devangshu/GripSimulator/esp8266/glove/glove.h

/* grip simulator glove device mqtt client driver */

#ifndef __GS_GLOVE_H__
#define __GS_GLOVE_H__

#define DEBUG true
#define DEBUG_VERBOSE true

#define WIFI_PASS "8372681759362047"

#define API_URL "mqtt.anuv.me"	// "test.mosquitto.org"
#define API_PORT 1883

#define DEVICE_NUM 0
#define DEVICE_NAME "glove"

#endif
