devangshu/GripSimulator/esp8266/model/model.h

/* grip simulator model device mqtt client driver */

#ifndef __GS_MODEL_H__
#define __GS_MODEL_H__

#define DEBUG false
#define DEBUG_VERBOSE false

#define WIFI_PASS "0335803293960677"

#define API_URL "mqtt.anuv.me"	// "test.mosquitto.org"
#define API_PORT 1883

#define DEVICE_NUM 1
#define DEVICE_NAME "model"

#endif
