devangshu/GripSimulator/tm4c123/inc/MAX5353.c

// MAX5353.c
// Runs on LM4F120/TM4C123
// Use SSI0 to send a 16-bit code to the MAX5353.
// Daniel Valvano
// September 11, 2013

/* This example accompanies the book
   "Embedded Systems: Real Time Interfacing to Arm Cortex M Microcontrollers",
   ISBN: 978-1463590154, Jonathan Valvano, copyright (c) 2015

 Copyright 2015 by Jonathan W. Valvano, valvano@mail.utexas.edu
    You may use, edit, run or distribute this file
    as long as the above copyright notice remains
 THIS SOFTWARE IS PROVIDED "AS IS".  NO WARRANTIES, WHETHER EXPRESS, IMPLIED
 OR STATUTORY, INCLUDING, BUT NOT LIMITED TO, IMPLIED WARRANTIES OF
 MERCHANTABILITY AND FITNESS FOR A PARTICULAR PURPOSE APPLY TO THIS SOFTWARE.
 VALVANO SHALL NOT, IN ANY CIRCUMSTANCES, BE LIABLE FOR SPECIAL, INCIDENTAL,
 OR CONSEQUENTIAL DAMAGES, FOR ANY REASON WHATSOEVER.
 For more information about my classes, my research, and my books, see
 http://users.ece.utexas.edu/~valvano/
 */

// SSI0Clk (SCLK, pin 4) connected to PA2
// SSI0Fss (!CS, pin 2) connected to PA3
// SSI0Tx (DIN, pin 3) connected to PA5
// see Figure 7.19 for complete schematic
#include <stdint.h>
#include "../inc/tm4c123gh6pm.h"


//********DAC_Init*****************
// Initialize Max5353 12-bit DAC
// inputs:  initial voltage output (0 to 4095)
// outputs: none
// assumes: system clock rate less than 20 MHz
void DAC_Init_Max(uint16_t data){
  SYSCTL_RCGCSSI_R |= 0x01;       // activate SSI0
  SYSCTL_RCGCGPIO_R |= 0x01;      // activate port A
  while((SYSCTL_PRGPIO_R&0x01) == 0){};// ready?
  GPIO_PORTA_AFSEL_R |= 0x2C;     // enable alt funct on PA2,3,5
  GPIO_PORTA_DEN_R |= 0x2C;       // configure PA2,3,5 as SSI
  GPIO_PORTA_PCTL_R = (GPIO_PORTA_PCTL_R&0xFF0F00FF)+0x00202200;
  GPIO_PORTA_AMSEL_R = 0;         // disable analog functionality on PA
  SSI0_CR1_R = 0x00000000;        // disable SSI, master mode
  SSI0_CPSR_R = 0x02;             // 8 MHz SSIClk 
  SSI0_CR0_R &= ~(0x0000FFF0);    // SCR = 0, SPH = 0, SPO = 0 Freescale
  SSI0_CR0_R |= 0x0F;             // DSS = 16-bit data
  SSI0_DR_R = data;               // load 'data' into transmit FIFO
  SSI0_CR1_R |= 0x00000002;       // enable SSI

}

//********DAC_Init*****************
// Initialize TLV5616 12-bit DAC
// assumes bus clock is 80 MHz
// inputs: initial voltage output (0 to 4095)
// outputs:none

void DAC_Init(uint16_t data){
  SYSCTL_RCGCSSI_R |= 0x02;       // activate SSI1
  SYSCTL_RCGCGPIO_R |= 0x08;      // activate port D
  
  while((SYSCTL_PRGPIO_R&0x08) == 0){}; // ready?
  SSI1_CR1_R = 0x00000000;        // disable SSI, master mode
  GPIO_PORTD_AFSEL_R |= 0x0B;     // enable alt funct on PD3,1,0
  GPIO_PORTD_DEN_R |= 0x0B;       // enable digital I/O on PD3,1,0
  GPIO_PORTD_PCTL_R = (GPIO_PORTD_PCTL_R
                     & 0xFFFF0F00)
                     + 0x00002022;
  GPIO_PORTD_AMSEL_R &= ~0x0B;    // disable analog functionality on PD
  SSI1_CPSR_R = 0x08;             // 80MHz/8 = 10 MHz SSIClk (should work up to 20 MHz)
  SSI1_CR0_R &= ~(0x0000FFF0);    // SCR = 0, SPH = 0, SPO = 1 Freescale
  SSI1_CR0_R += 0x40;             // SPO = 1
  SSI1_CR0_R |= 0x0F;             // DSS = 16-bit data
  SSI1_DR_R = data;               // load 'data' into transmit FIFO
  SSI1_CR1_R |= 0x00000002;       // enable SSI
}




//********DAC_Out*****************
// Send data to Max5353 12-bit DAC
// inputs:  voltage output (0 to 4095)
// outputs: none
void DAC_Out(uint16_t code){   
  while((SSI1_SR_R&0x00000002)==0){};// SSI Transmit FIFO Not Full
  SSI1_DR_R = code; }                // data out, no reply
  
//********DAC_Out*****************
// Send data to Max5353 12-bit DAC
// inputs:  voltage output (0 to 4095)
// outputs: reply is returned
// send the 16-bit code to the SSI, return a reply
uint16_t DAC_Out2(uint16_t code){   uint16_t receive;
  while((SSI0_SR_R&0x00000002)==0){};// SSI Transmit FIFO Not Full
  SSI0_DR_R = code;                  // data out
  while((SSI0_SR_R&0x00000004)==0){};// SSI Receive FIFO Not Empty
  receive = SSI0_DR_R;               // acknowledge response
  return receive;
}

void DAC_InitRaw(void){
  SYSCTL_RCGCSSI_R |= 0x01;       // activate SSI0
  SYSCTL_RCGCGPIO_R |= 0x01;      // activate port A
  while((SYSCTL_PRGPIO_R&0x01) == 0){};// ready?
  GPIO_PORTA_AFSEL_R |= 0x24;     // enable alt funct on PA2,5, regular GPIO on PA3
  GPIO_PORTA_DEN_R |= 0x2C;       // configure PA2,5 as SSI, PA3 is regular GPIO
  GPIO_PORTA_DATA_R |= 0x08;      // PA3 FSS high
  GPIO_PORTA_PCTL_R = (GPIO_PORTA_PCTL_R&0xFF0F00FF)+0x00200200;
  GPIO_PORTA_AMSEL_R = 0;         // disable analog functionality on PA
  SSI0_CR1_R = 0x00000000;        // disable SSI, master mode
  SSI0_CPSR_R = 0x02;             // 8 MHz SSIClk 
  SSI0_CR0_R &= ~(0x0000FFF0);    // SCR = 0, SPH = 0, SPO = 0 Freescale
  SSI0_CR0_R |= 0x0F;             // DSS = 16-bit data
  SSI0_CR1_R |= 0x00000002;       // enable SSI

}
//********DAC_Out*****************
// Send data to Max5353 12-bit DAC
// inputs:  voltage output (0 to 4095)
// outputs: none
// send the 16-bit code to the SSI, 
void DAC_OutRaw(uint16_t code){  
  GPIO_PORTA_DATA_R &= ~0x08;        // PA3 FSS low
  
  while((SSI0_SR_R&0x00000002)==0){};// SSI Transmit FIFO Not Full
  SSI0_DR_R = code;                  // data out

  GPIO_PORTA_DATA_R |= 0x08;         // PA3 FSS high
}
