devangshu/GripSimulator/esp8266/common.h

/* grip simulator common device client config */

#ifndef __GS_COMMON_H__
#define __GS_COMMON_H__

#include <Arduino.h>
#include <ESP8266WiFi.h>
#include <NTPClient.h>
#include <PubSubClient.h>
#include <WiFiUdp.h>

//#define WIFI_SSID "21 Resident"
//#define WIFI_PASS "Hookem*2101"
#define WIFI_SSID "utexas-iot"

#define TIME_SERVER "pool.ntp.org"
#define MQTT_CLIENT_ID "gripsim_445l_client"

#define VIRTUALPIN_COUNT 5
#define VIRTUALPIN_TOPIC "virtualpin"
#define VIRTUALPIN_TOPIC_LEN 10

#define MSGBUFF_MAXLEN 500

#define BRIGHTNESS_MIN 0
#define BRIGHTNESS_MAX PWMRANGE	 // 1023 or 255

/* utilities */
// generic
int bound_integer(int value, int minimum, int maximum) {
	if (value < minimum) value = minimum;
	if (value > maximum) value = maximum;
	return value;
}
// led control
int correct_brightness(int brightness) {
	return bound_integer(brightness, BRIGHTNESS_MIN, BRIGHTNESS_MAX);
}
void led_out(int led_pin, int brightness) {
	brightness = correct_brightness(brightness);
	analogWrite(led_pin, brightness);
}
void led_out_builtin(int led_b_pin, int brightness) {
	brightness = correct_brightness(brightness);
	brightness = BRIGHTNESS_MAX - (brightness - BRIGHTNESS_MIN);
	analogWrite(led_b_pin, brightness);
}

#endif
