devangshu/GripSimulator/tm4c123/src/GripSimulator-Glove/TimerDriver.c

/* Timer Driver Module */

#include "TimerDriver.h"

/* constants */

#define PF1 (*((volatile uint32_t *)0x40025008))
#define PF2 (*((volatile uint32_t *)0x40025010))

/* module direct imports */

/* module fields */

/* module internal functions */

void Timer0_Init(void) {
	volatile uint32_t delay;
	// **** general initialization ****
	SYSCTL_RCGCTIMER_R |= 0x01;		  // activate timer0
	delay = SYSCTL_RCGCTIMER_R;		  // allow time to finish activating
	TIMER0_CTL_R &= ~TIMER_CTL_TAEN;  // disable timer0A during setup
	TIMER0_CFG_R = 0;				  // configure for 32-bit timer mode
	// **** timer0A initialization ****
	// configure for periodic mode
	TIMER0_TAMR_R = TIMER_TAMR_TAMR_PERIOD;
	TIMER0_TAILR_R = (80000 / 2) - 1;
	TIMER0_IMR_R |= TIMER_IMR_TATOIM;	// enable timeout (rollover) interrupt
	TIMER0_ICR_R = TIMER_ICR_TATOCINT;	// clear timer0A timeout flag
										//TIMER0_TAPR_R = 0;
	TIMER0_CTL_R |= TIMER_CTL_TAEN;		// enable timer0A 32-b, periodic, interrupts
	// **** interrupt initialization ****
	// Timer0A=priority 2
	NVIC_PRI4_R = (NVIC_PRI4_R & 0x00FFFFFF) | 0x40000000;	// top 3 bits
	NVIC_EN0_R = 1 << 19;									// enable interrupt 19 in NVIC
}
void Timer0A_Init100HzInt(void) {
	volatile uint32_t delay;
	// **** general initialization ****
	SYSCTL_RCGCTIMER_R |= 0x01;		  // activate timer0
	delay = SYSCTL_RCGCTIMER_R;		  // allow time to finish activating
	TIMER0_CTL_R &= ~TIMER_CTL_TAEN;  // disable timer0A during setup
	TIMER0_CFG_R = 0;				  // configure for 32-bit timer mode
	// **** timer0A initialization ****
	// configure for periodic mode
	TIMER0_TAMR_R = TIMER_TAMR_TAMR_PERIOD;
	TIMER0_TAILR_R = 799999;			// start value for 100 Hz interrupts
	TIMER0_IMR_R |= TIMER_IMR_TATOIM;	// enable timeout (rollover) interrupt
	TIMER0_ICR_R = TIMER_ICR_TATOCINT;	// clear timer0A timeout flag
	TIMER0_CTL_R |= TIMER_CTL_TAEN;		// enable timer0A 32-b, periodic, interrupts
	// **** interrupt initialization ****
	// Timer0A=priority 2
	NVIC_PRI4_R = (NVIC_PRI4_R & 0x00FFFFFF) | 0x40000000;	// top 3 bits
	NVIC_EN0_R = 1 << 19;									// enable interrupt 19 in NVIC
}
void Timer1_Init(void) {
	volatile uint32_t delay;
	SYSCTL_RCGCTIMER_R |= 0x02;								// 0) activate TIMER1
	delay = SYSCTL_RCGCTIMER_R;								// allow time to finish activating
	TIMER1_CTL_R = 0x00000000;								// 1) disable TIMER1A during setup
	TIMER1_CFG_R = 0x00000000;								// 2) configure for 32-bit mode
	TIMER1_TAMR_R = 0x00000002;								// 3) configure for periodic mode, down-count
	TIMER1_TAILR_R = 80000000;								// 4) reload value
	TIMER1_TAPR_R = 0;										// 5) bus clock resolution
	TIMER1_ICR_R = 0x00000001;								// 6) clear TIMER1A timeout flag
	TIMER1_IMR_R = 0x00000001;								// 7) arm timeout interrupt
	NVIC_PRI5_R = (NVIC_PRI5_R & 0xFFFF00FF) | 0x00008000;	// ?? priority 4
	NVIC_EN0_R = 1 << 21;									// 9) enable IRQ 21 in NVIC
	TIMER1_CTL_R = 0x00000001;								// 10) enable TIMER1A
}
/*
void Timer2_Init(void){
	SYSCTL_RCGCTIMER_R |= 0x04;   // 0) activate timer2
  TIMER2_CTL_R = 0x00000000;    // 1) disable timer2A during setup
  TIMER2_CFG_R = 0x00000000;    // 2) configure for 32-bit mode
  TIMER2_TAMR_R = 0x00000002;   // 3) configure for periodic mode, default down-count settings
  TIMER2_TAILR_R = 80000-1;    // 4) reload value
  TIMER2_TAPR_R = 0;            // 5) bus clock resolution
  TIMER2_ICR_R = 0x00000001;    // 6) clear timer2A timeout flag
  TIMER2_IMR_R = 0x00000001;    // 7) arm timeout interrupt
  NVIC_PRI5_R = (NVIC_PRI5_R&0x00FFFFFF)|(1<<29); // priority  
// interrupts enabled in the main program after all devices initialized
// vector number 39, interrupt number 23
  NVIC_EN0_R = 1<<23;           // 9) enable IRQ 23 in NVIC
  TIMER2_CTL_R = 0x00000001;    // 10) enable timer2A
	
	Audio_SetTone(tone_id);
	
}
*/

/*
void Timer0A_Handler(void) {
	TIMER0_ICR_R = TIMER_ICR_TATOCINT;	// acknowledge timer0A timeout

	//PF2 ^= 0x04;                   // profile

	//Switches_Loop();
	//Timer_HandleAlarm();

	//uint32_t time_measurement = TIMER1_TAR_R;
}
*/

/*
void Timer1A_Handler(void) {
	TIMER1_ICR_R = TIMER_ICR_TATOCINT;	// acknowledge TIMER1A timeout

	// timer1A
}
*/

/*
void Timer2A_Handler(void){

    TIMER2_ICR_R = TIMER_ICR_TATOCINT;    // acknowledge timer2 timeout

    // timer2A

    //PF2 ^= 0x04;
}
*/

uint32_t get_time_measurement(void) {
	uint32_t time_measurement = TIMER1_TAR_R;
	return time_measurement;
}

/* module external methods */

void Timer_SetTask2(void (*task2)(void), uint32_t period) {
	Timer2_Init(task2, period);	 // 100Hz
}

void Timer_SetTask3(void (*task3)(void), uint32_t period) {
	Timer3_Init(task3, period);
}

void Timer_Init() {
	//Timer0_Init();
	//Timer0A_Init100HzInt();
	//Timer1_Init();
	//Timer2_Init();
	//Timer_InitTask3(timer_task);
}
